SamuelNoesslboeck/Bugsy/documentation/captures/4_monobodies.PNG

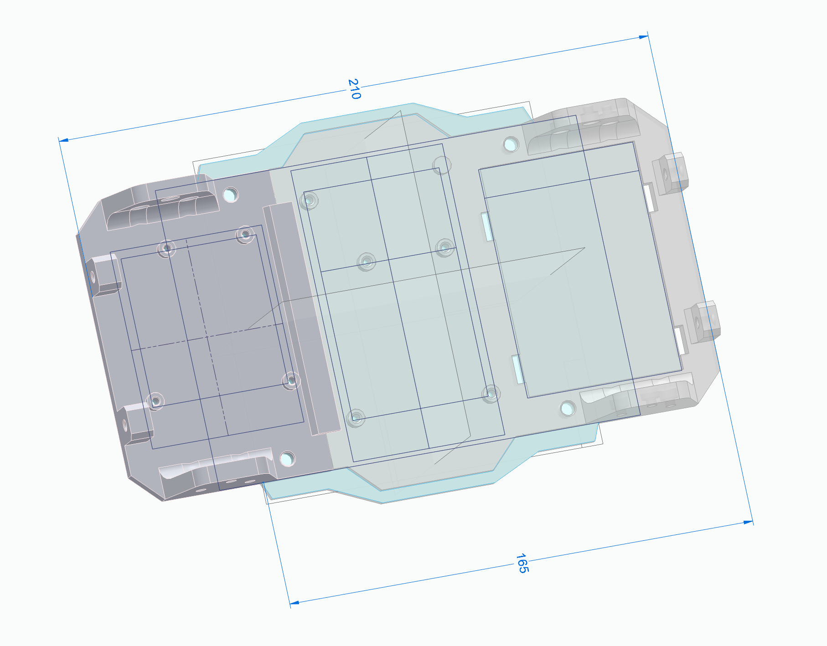
documentation/captures/4_monobodies.PNG
