SamuelNoesslboeck/Bugsy/documentation/captures/5_motor_side_frame.PNG

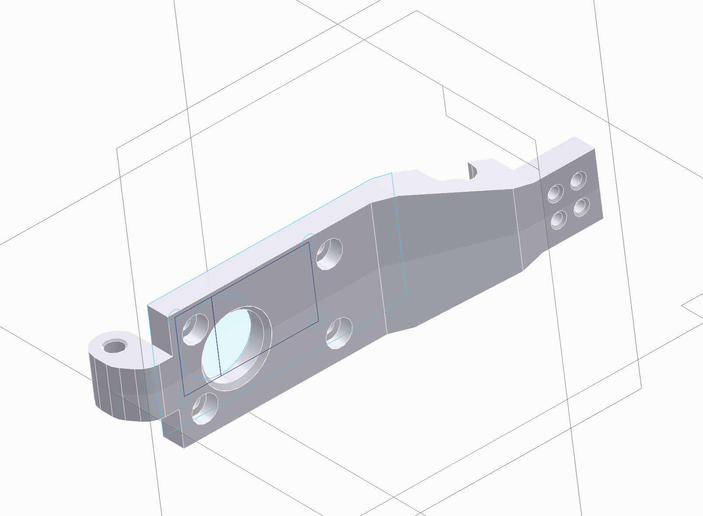
documentation/captures/5_motor_side_frame.PNG
