SamuelNoesslboeck/Bugsy/documentation/captures/6_motor_side_mounted.PNG

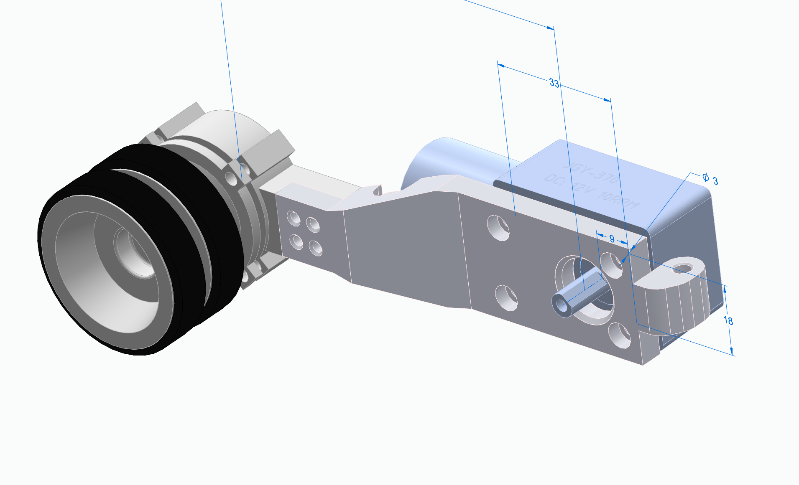
documentation/captures/6_motor_side_mounted.PNG
