SamuelNoesslboeck/Bugsy/documentation/captures/7_new_motor_plane.PNG

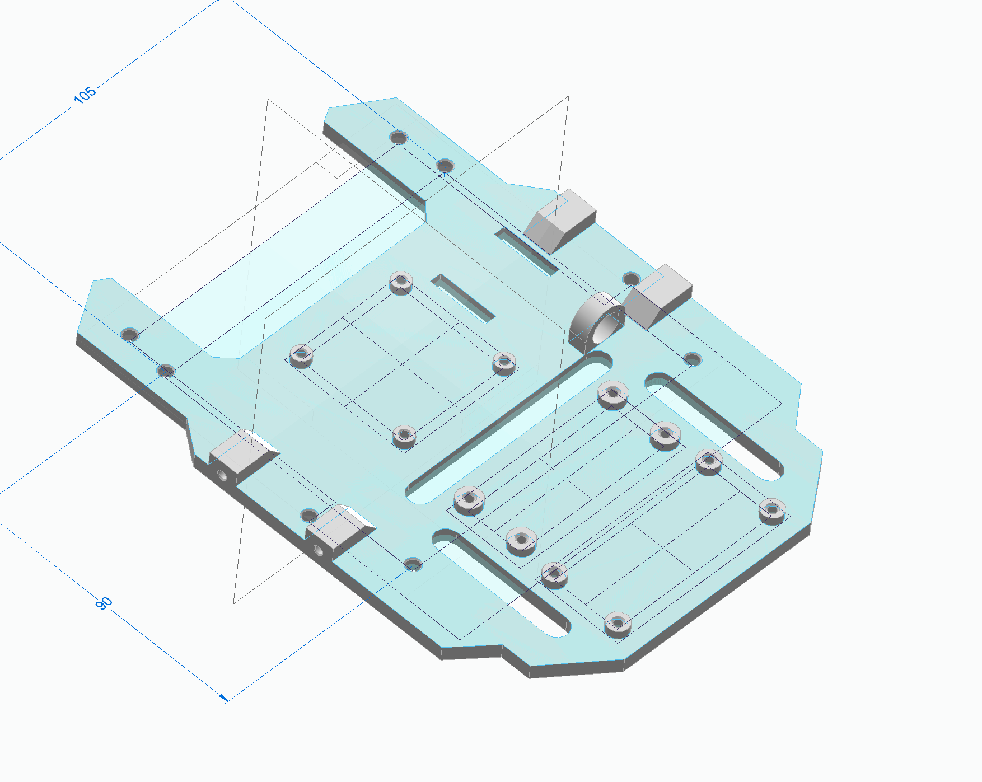
documentation/captures/7_new_motor_plane.PNG
