SamuelNoesslboeck/Bugsy/documentation/captures/8_reworked_motor_plane.PNG

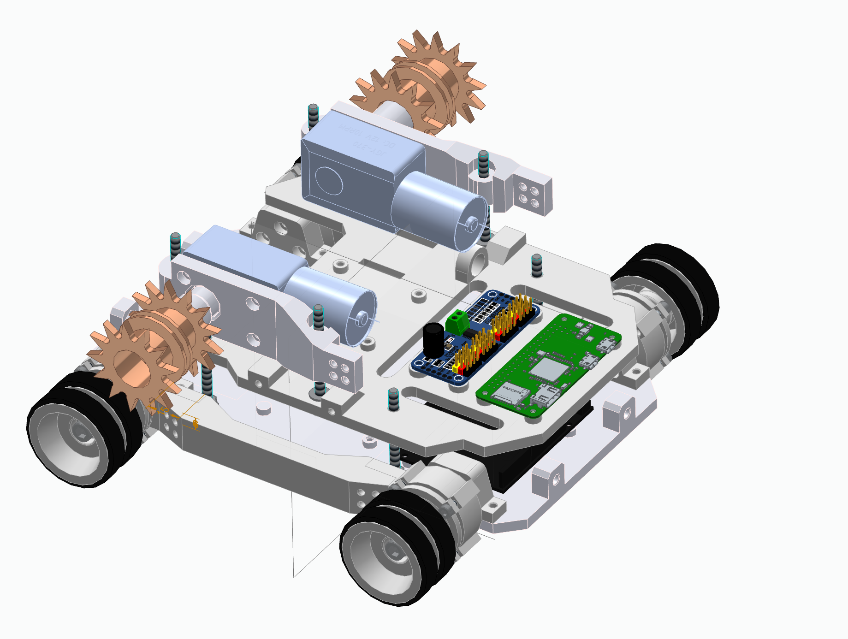
documentation/captures/8_reworked_motor_plane.PNG
