SamuelNoesslboeck/Bugsy/documentation/captures/9_further_shapegiving.png

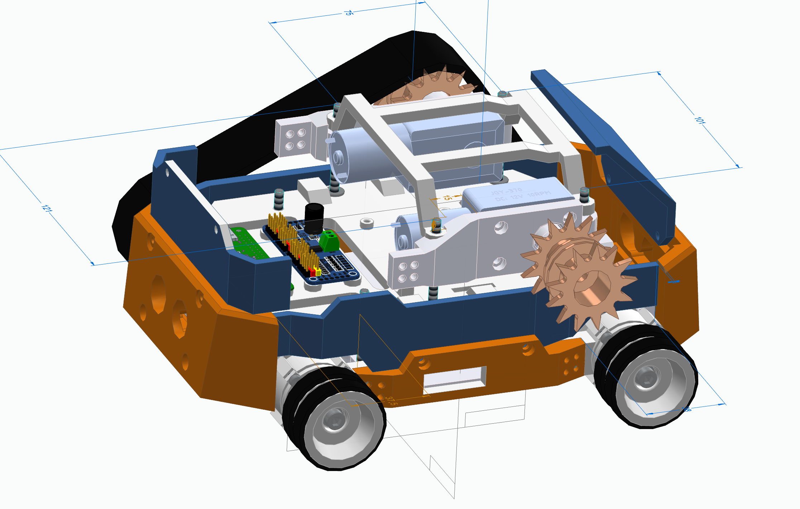
documentation/captures/9_further_shapegiving.png
